Cardinal-Space-Mining/2025-Comp-Arena/Arena/AgLime.jpg

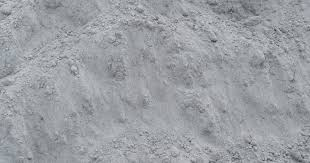
Arena/AgLime.jpg
