Cardinal-Space-Mining/2025-Comp-Arena/Arena/img/2x4s/2x4x80-HoleB.PNG

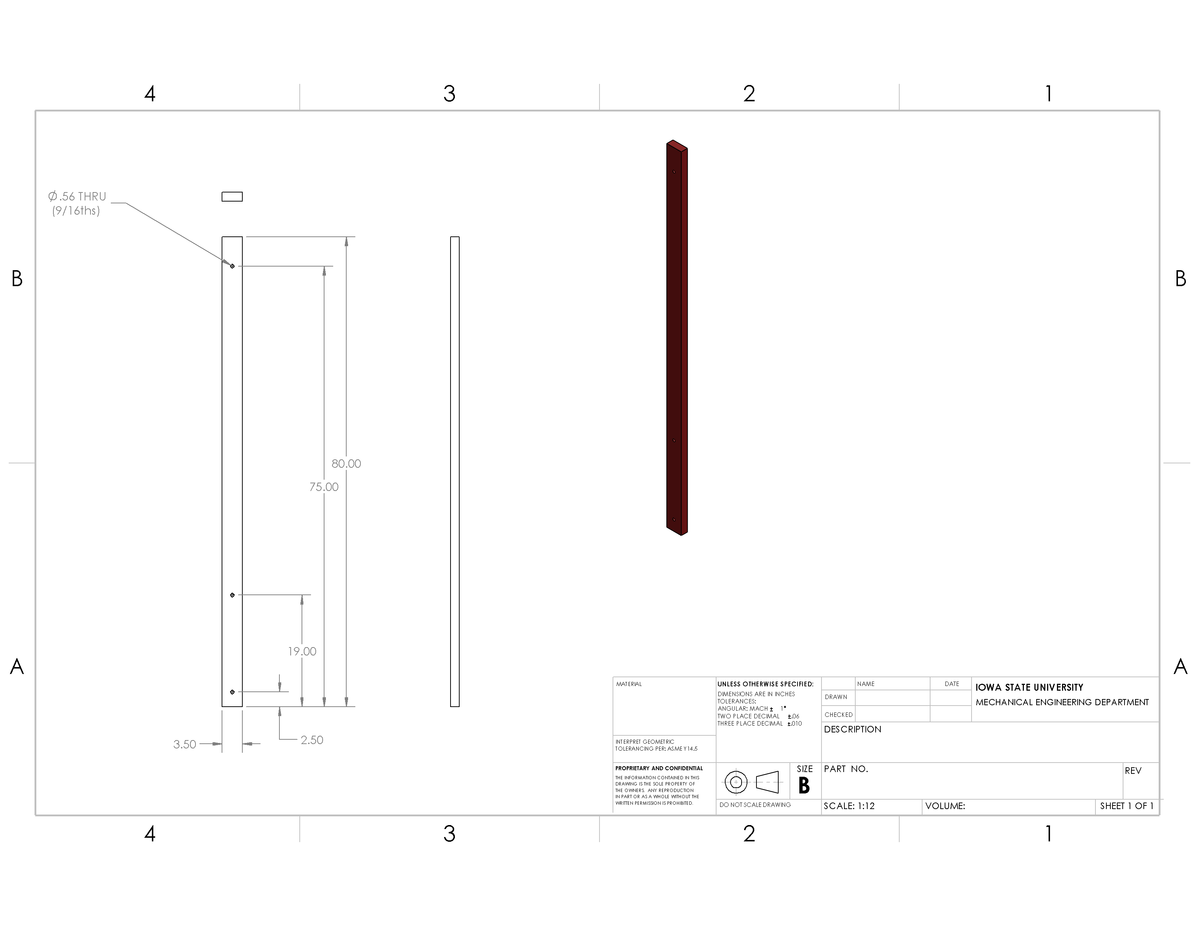
Arena/img/2x4s/2x4x80-HoleB.PNG
