Cardinal-Space-Mining/2025-Comp-Arena/HeiseSuggestions/Intake Air Filters.jpg

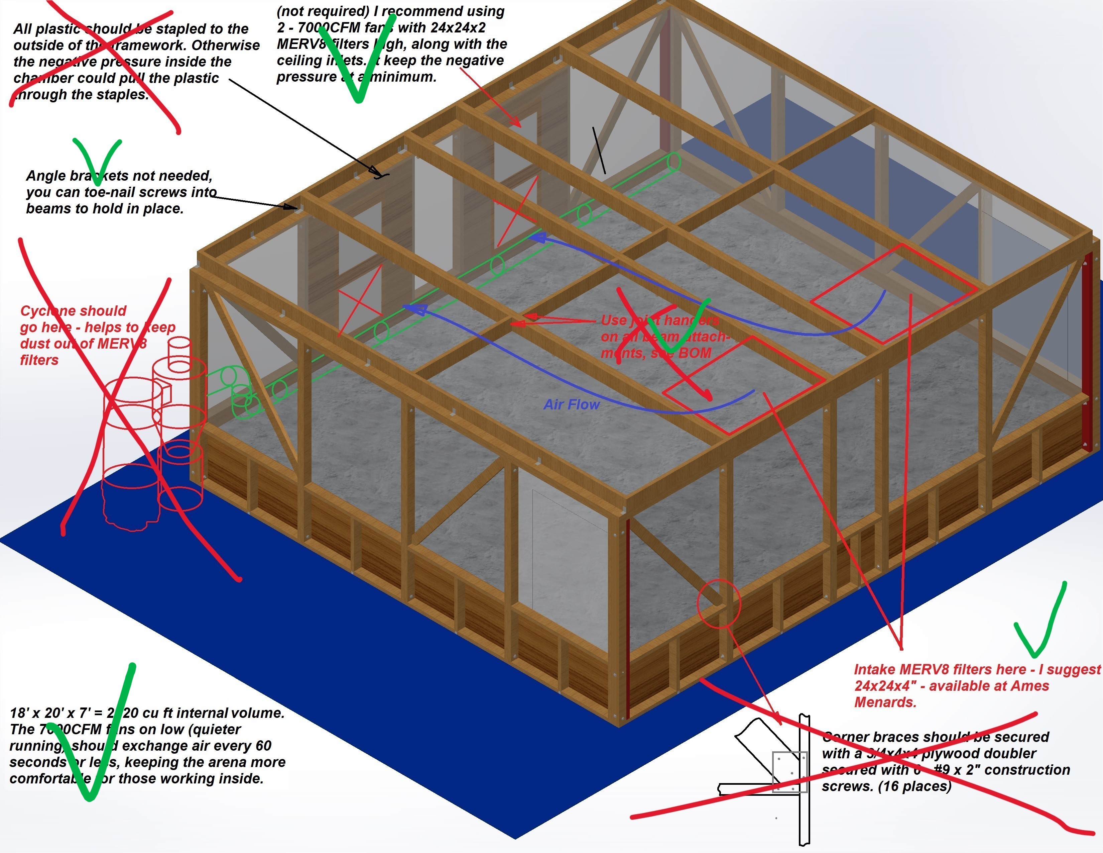
HeiseSuggestions/Intake Air Filters.jpg
