Cardinal-Space-Mining/2025-Comp-Arena/Arena/1x1s/1x1x2.SLDPRT

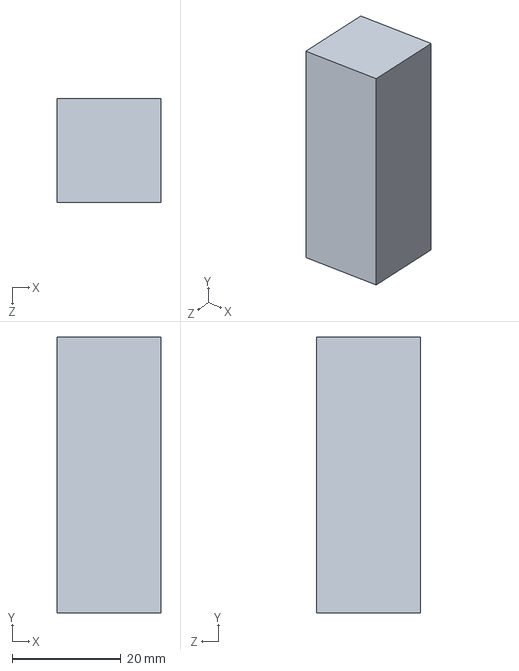
[picture p25: CAD file, 2025-01-25]
Arena/1x1s/1x1x2.SLDPRT
19.1 x 50.8 x 19.1 mm
