Cardinal-Space-Mining/2025-Comp-Arena/Arena/2x4s/2x4x80-HoleB.SLDPRT

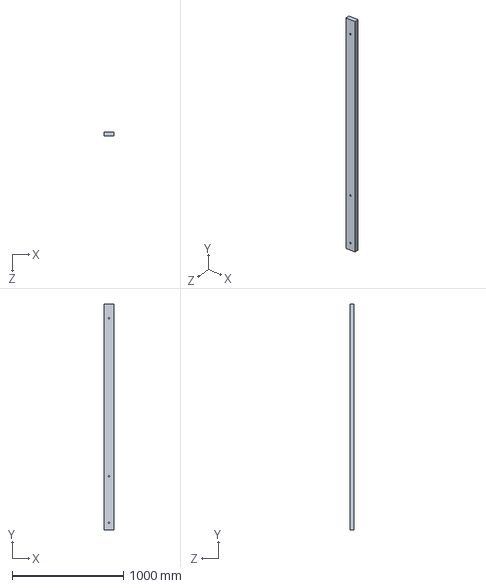
[picture p26: CAD file, 2025-03-30]
Arena/2x4s/2x4x80-HoleB.SLDPRT
88.9 x 2032.0 x 38.1 mm
