Cardinal-Space-Mining/2025-Comp-Arena/Arena/2x6s/2x6x21.SLDPRT

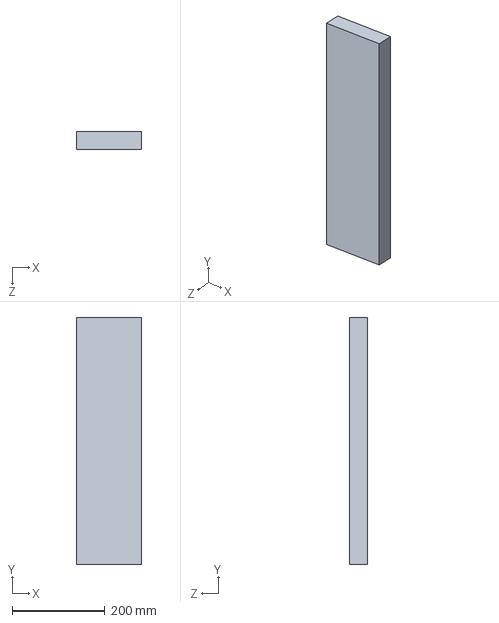
[picture p27: CAD file, 2025-03-01]
Arena/2x6s/2x6x21.SLDPRT
139.7 x 533.4 x 38.1 mm
