Cardinal-Space-Mining/2025-Comp-Arena/Arena/4x4s/4x4x83.SLDPRT

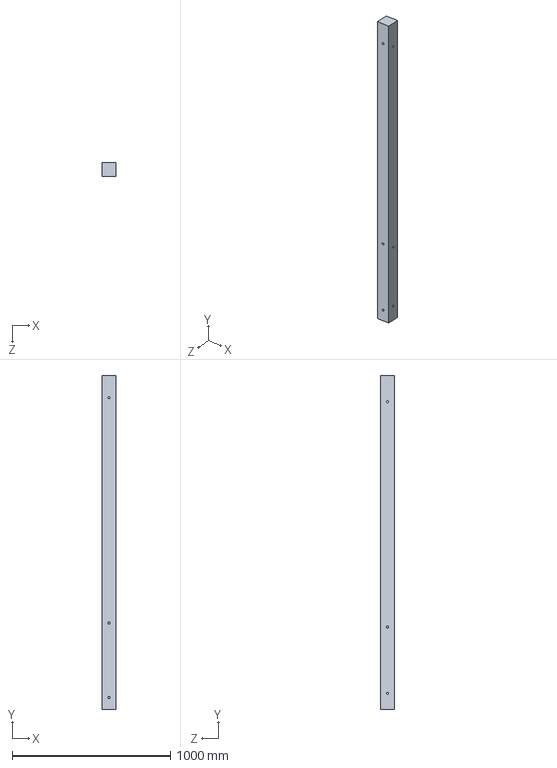
[picture p28: CAD file, 2025-03-30]
Arena/4x4s/4x4x83.SLDPRT
88.9 x 2108.2 x 88.9 mm
