Cardinal-Space-Mining/2025-Comp-Arena/Arena/filters/45x21 MERV8 Filter.SLDPRT

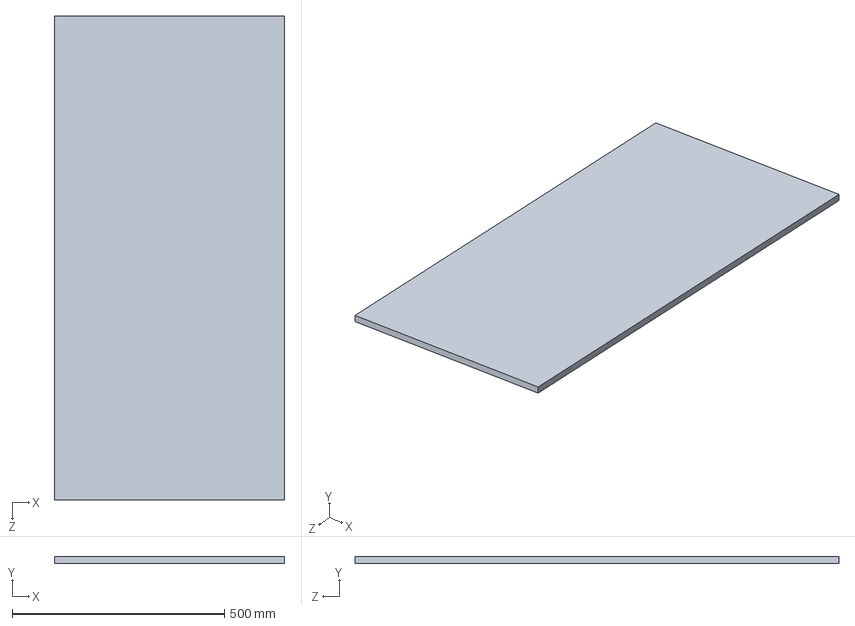
[picture p29: CAD file, 2025-05-02]
Arena/filters/45x21 MERV8 Filter.SLDPRT
541.3 x 16.5 x 1138.2 mm
