Cardinal-Space-Mining/2025-Comp-Arena/Arena/particle board/pbx24x96 particle board.SLDPRT

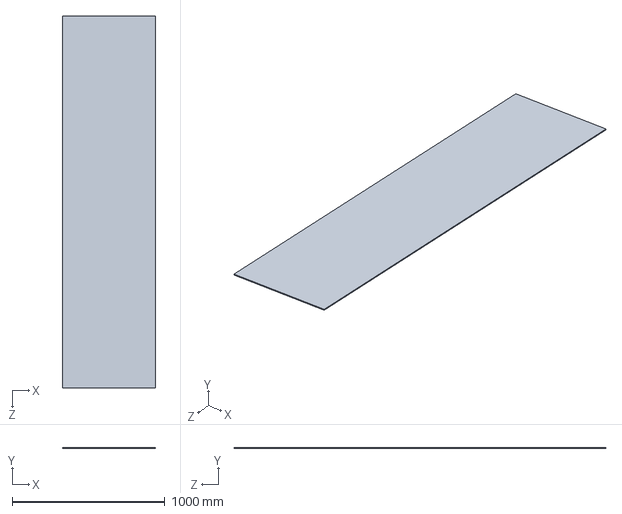
[picture p30: CAD file, 2025-03-01]
Arena/particle board/pbx24x96 particle board.SLDPRT
609.6 x 5.56 x 2438.4 mm
