Cardinal-Space-Mining/2025-Comp-Arena/Arena/plywood/plywoodx82.7x48.SLDPRT

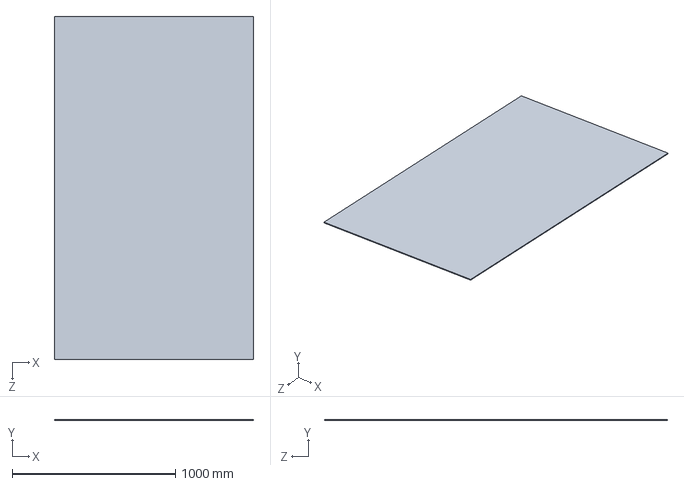
[picture p31: CAD file, 2025-05-02]
Arena/plywood/plywoodx82.7x48.SLDPRT
1219.2 x 5.56 x 2100.6 mm
