Cardinal-Space-Mining/2025-Comp-Arena/Arena/SICK/V3S##2-######A-S249638.SLDPRT

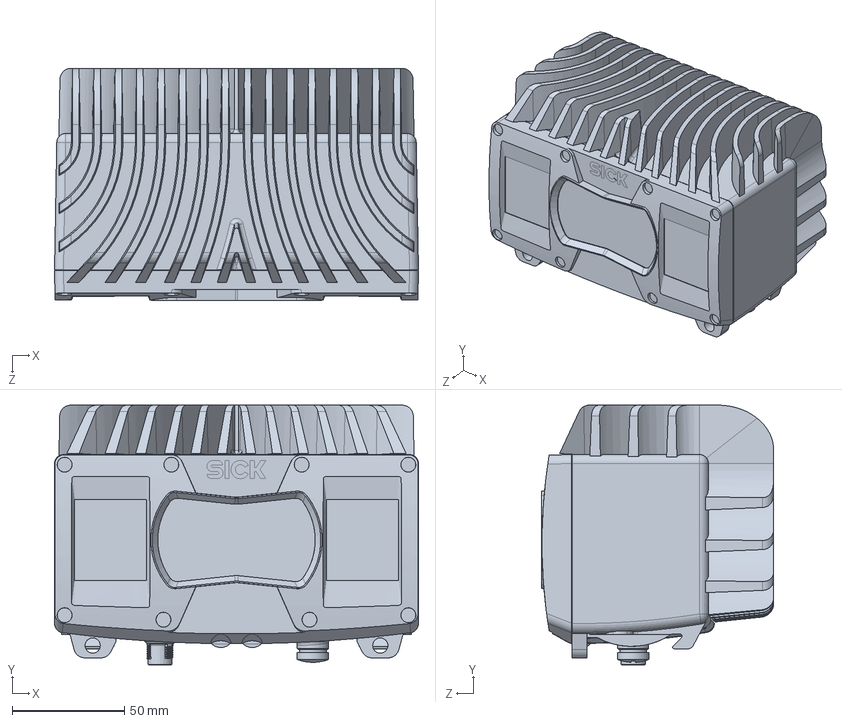
[picture p32: CAD file, 2025-03-29]
Arena/SICK/V3S##2-######A-S249638.SLDPRT
162.0 x 115.6 x 103.4 mm
