Cardinal-Space-Mining/2025-Comp-Arena/Arena/SICK_3DP_Depth_Camera_Mount.SLDPRT

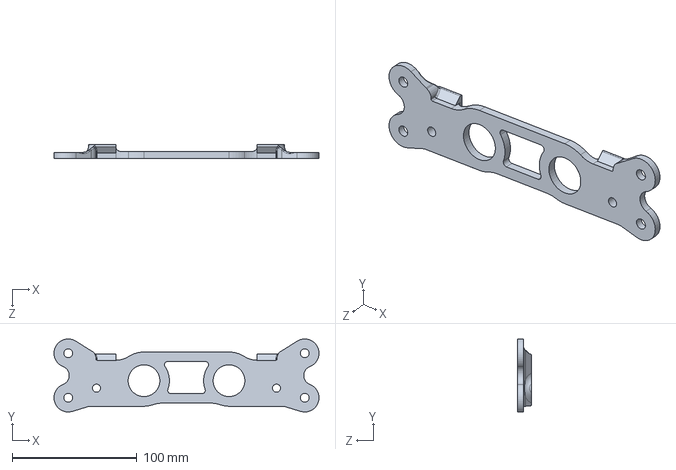
[picture p33: CAD file, 2025-05-20]
Arena/SICK_3DP_Depth_Camera_Mount.SLDPRT
212.0 x 58.4 x 11.0 mm
