Cardinal-Space-Mining/2025-Comp-Arena/Arena/strongtie/lu24.SLDPRT

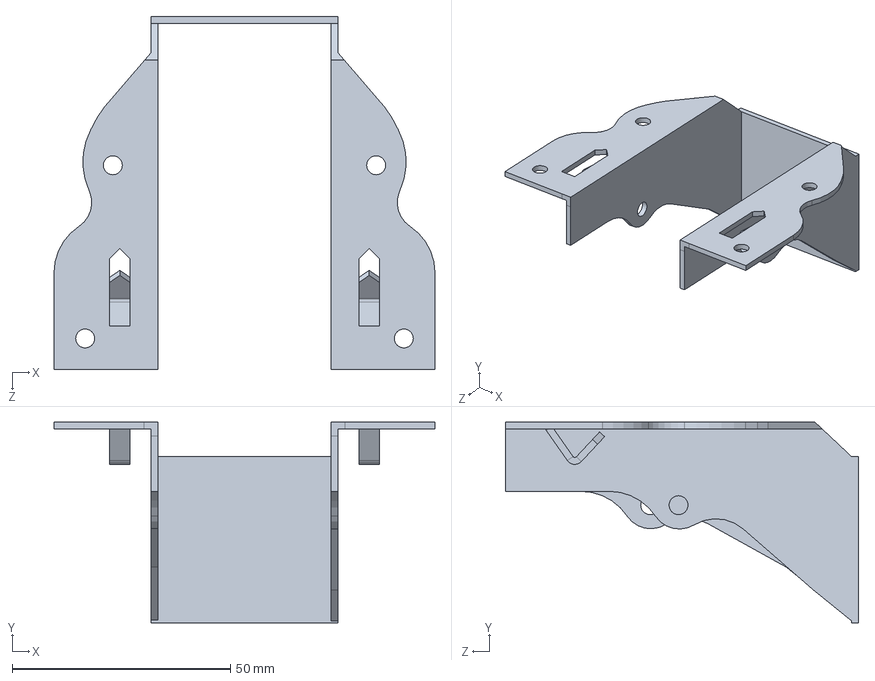
[picture p34: CAD file, 2025-05-02]
Arena/strongtie/lu24.SLDPRT
87.3 x 46.0 x 81.0 mm
