Cardinal-Space-Mining/2025-Comp-Arena/Arena/tie straps/Tie Strap 199in.SLDPRT

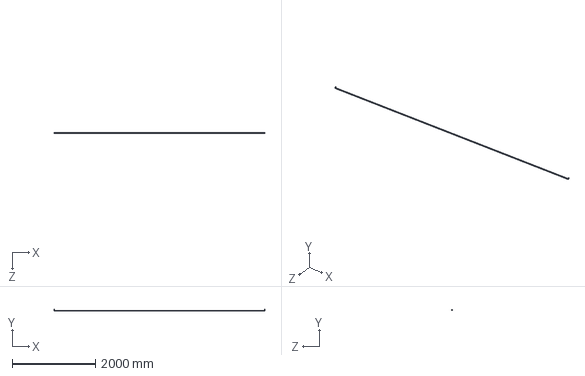
[picture p35: CAD file, 2025-03-08]
Arena/tie straps/Tie Strap 199in.SLDPRT
5055.1 x 25.7 x 25.4 mm
