Cardinal-Space-Mining/2025-Comp-Arena/Arena/vapor barriers/30x20ft Tarp.SLDPRT

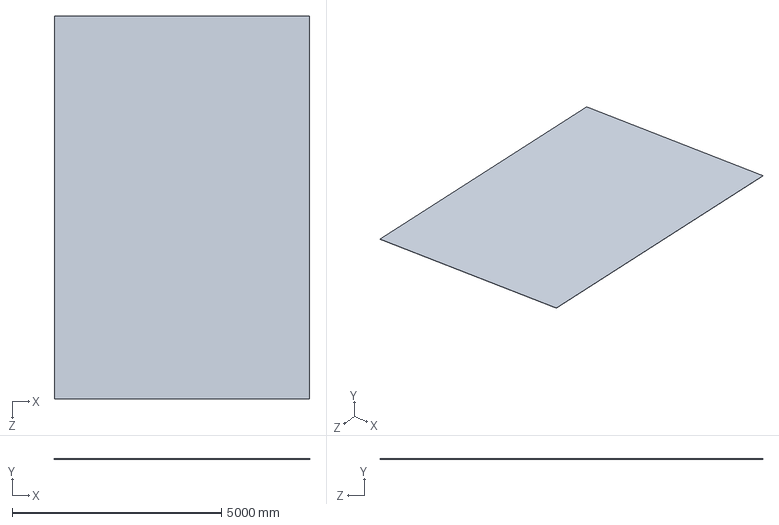
[picture p36: CAD file, 2025-03-30]
Arena/vapor barriers/30x20ft Tarp.SLDPRT
6096.0 x 6.00 x 9144.0 mm
