Cardinal-Space-Mining/2025-Comp-Arena/Arena/weatherproofing/Half Inch Weather Stripping.SLDPRT

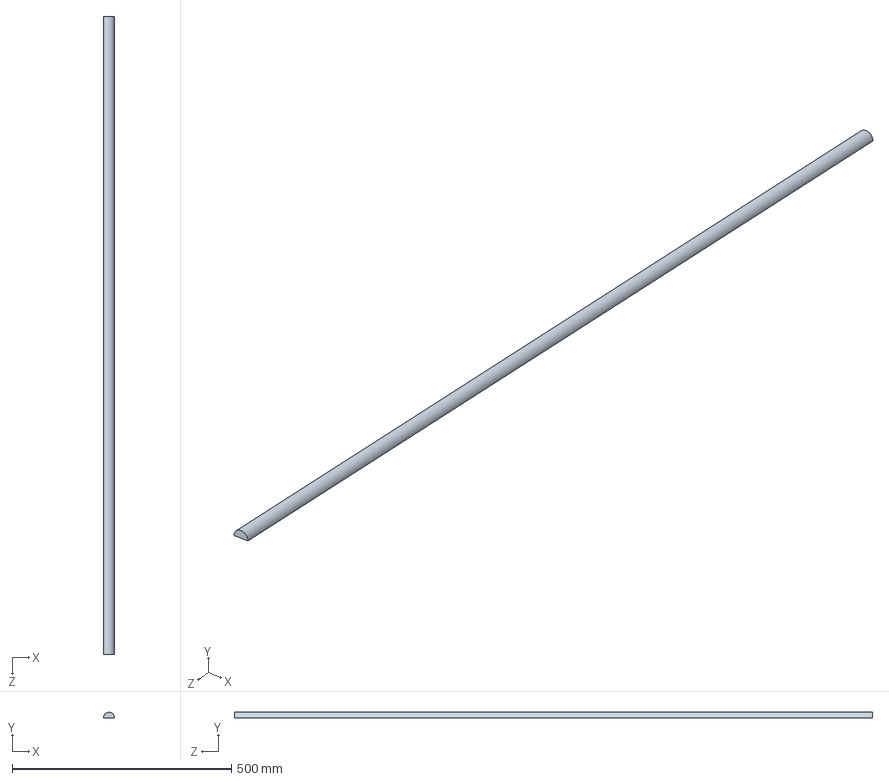
[picture p37: CAD file, 2025-01-21]
Arena/weatherproofing/Half Inch Weather Stripping.SLDPRT
25.4 x 12.7 x 1454.1 mm
