Cardinal-Space-Mining/2025-Comp-Arena/Arena/1x1s/1x1x20.11.SLDPRT

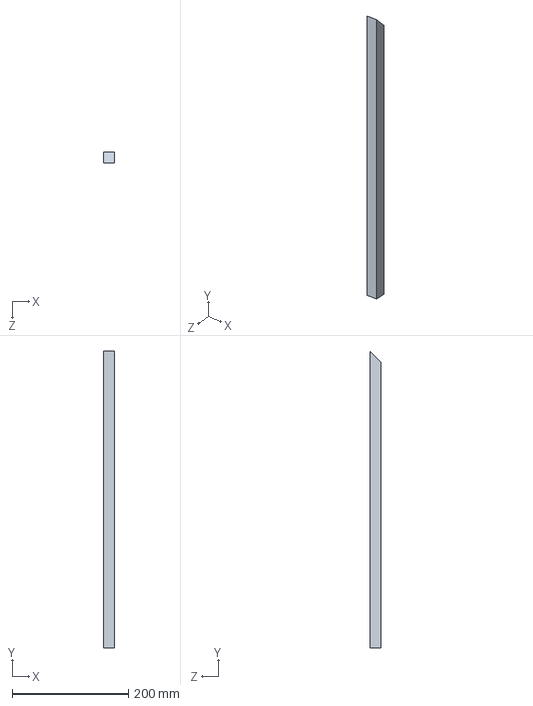
[picture p38: CAD file, 2025-01-25]
Arena/1x1s/1x1x20.11.SLDPRT
19.1 x 510.8 x 19.1 mm
