Cardinal-Space-Mining/2025-Comp-Arena/Arena/2x6s/2x6x223-Chamfered.SLDPRT

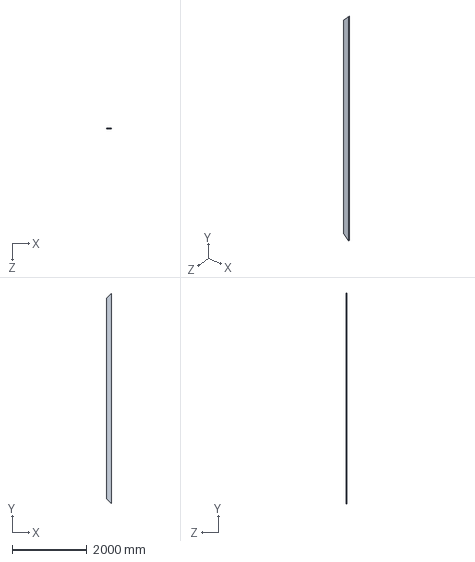
[picture p39: CAD file, 2025-03-01]
Arena/2x6s/2x6x223-Chamfered.SLDPRT
139.7 x 5664.2 x 38.1 mm
