Cardinal-Space-Mining/2025-Comp-Arena/Arena/4x4s/4x4x91.5.SLDPRT

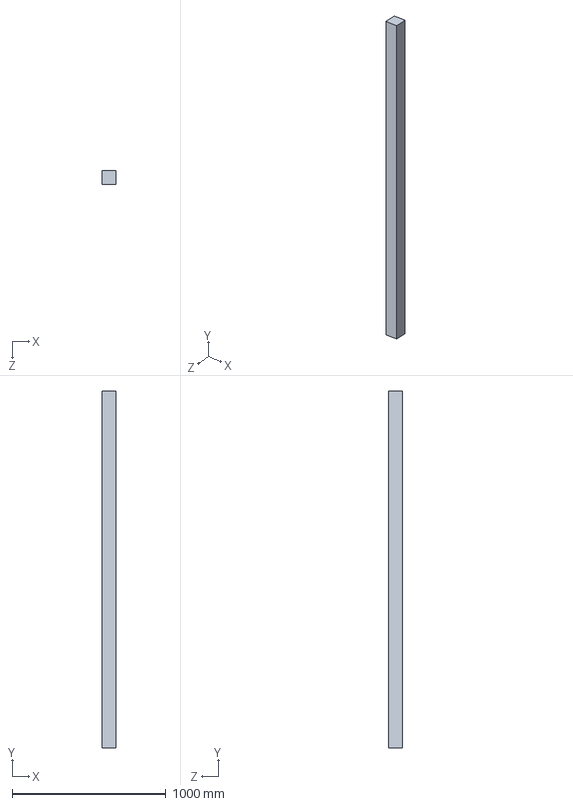
[picture p40: CAD file, 2025-01-21]
Arena/4x4s/4x4x91.5.SLDPRT
88.9 x 2324.1 x 88.9 mm
