Cardinal-Space-Mining/2025-Comp-Arena/Arena/filters/24x24 MERV8 Filter.SLDPRT

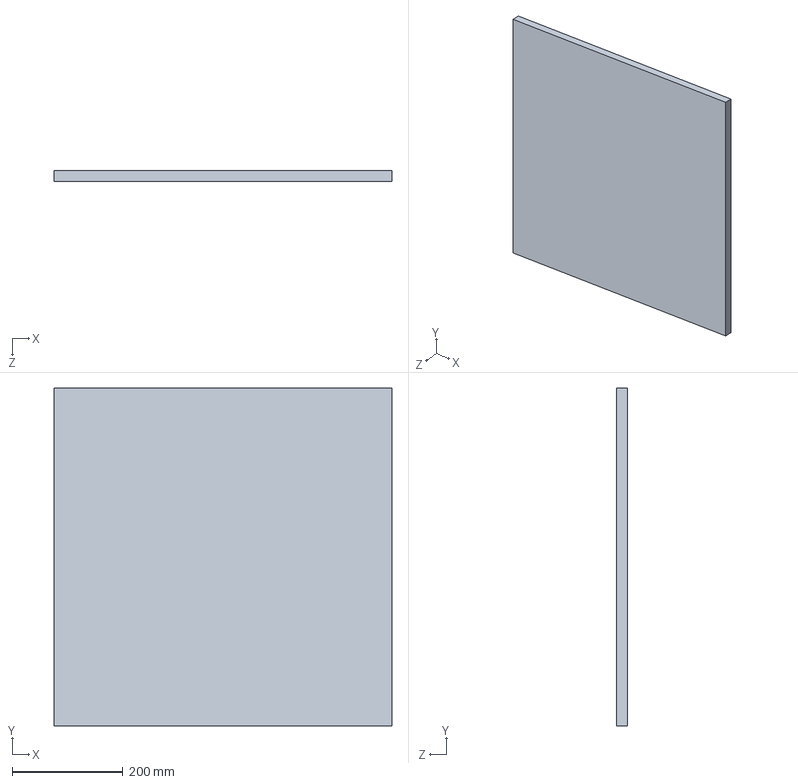
[picture p41: CAD file, 2025-01-21]
Arena/filters/24x24 MERV8 Filter.SLDPRT
609.6 x 609.6 x 19.1 mm
