Cardinal-Space-Mining/2025-Comp-Arena/Arena/plywood/plywoodx48x23.7 plywood.SLDPRT

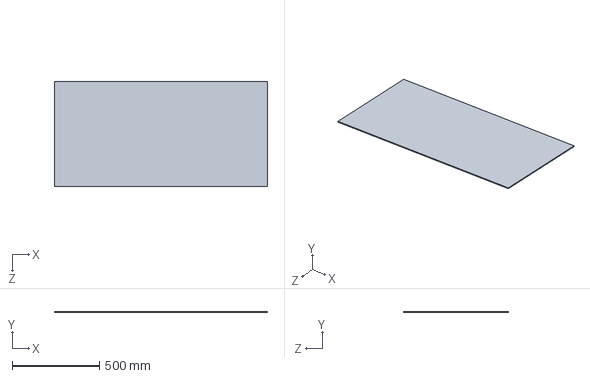
[picture p43: CAD file, 2025-03-30]
Arena/plywood/plywoodx48x23.7 plywood.SLDPRT
1219.2 x 5.56 x 602.0 mm
