Cardinal-Space-Mining/2025-Comp-Arena/Arena/strongtie/lu26.SLDPRT

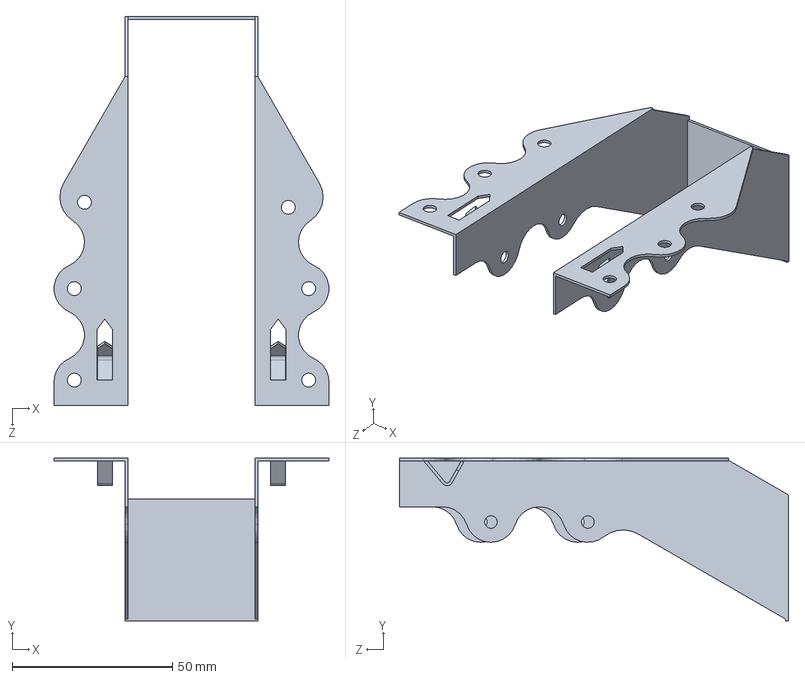
[picture p44: CAD file, 2025-05-02]
Arena/strongtie/lu26.SLDPRT
85.9 x 50.8 x 121.5 mm
