Cardinal-Space-Mining/2025-Comp-Arena/Arena/tie straps/Tie Strap 223in.SLDPRT

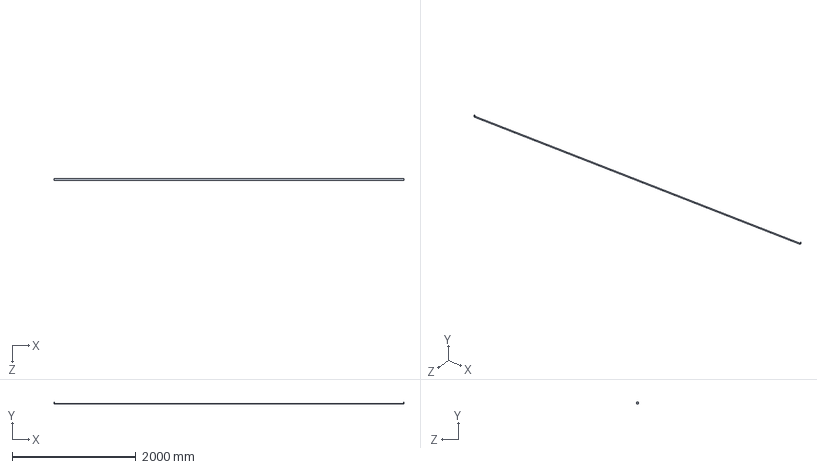
[picture p45: CAD file, 2025-03-08]
Arena/tie straps/Tie Strap 223in.SLDPRT
5664.7 x 25.7 x 25.4 mm
