Cardinal-Space-Mining/2025-Comp-Arena/Arena/vapor barriers/LZipperDoor.SLDPRT

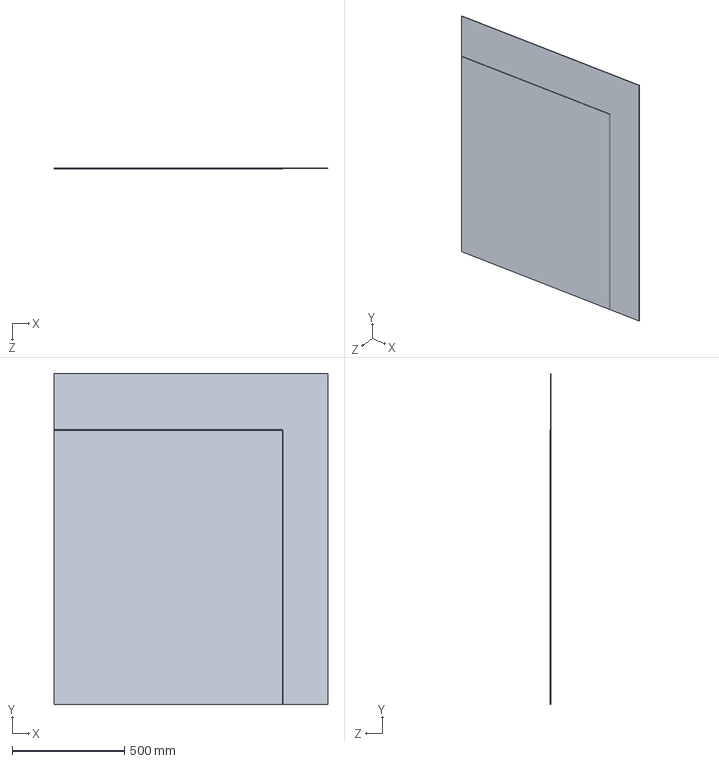
[picture p46: CAD file, 2025-03-08]
Arena/vapor barriers/LZipperDoor.SLDPRT
1219.2 x 1473.2 x 3.81 mm
