Cardinal-Space-Mining/2025-Comp-Arena/Arena/weatherproofing/Sprayfoam Seal.SLDPRT

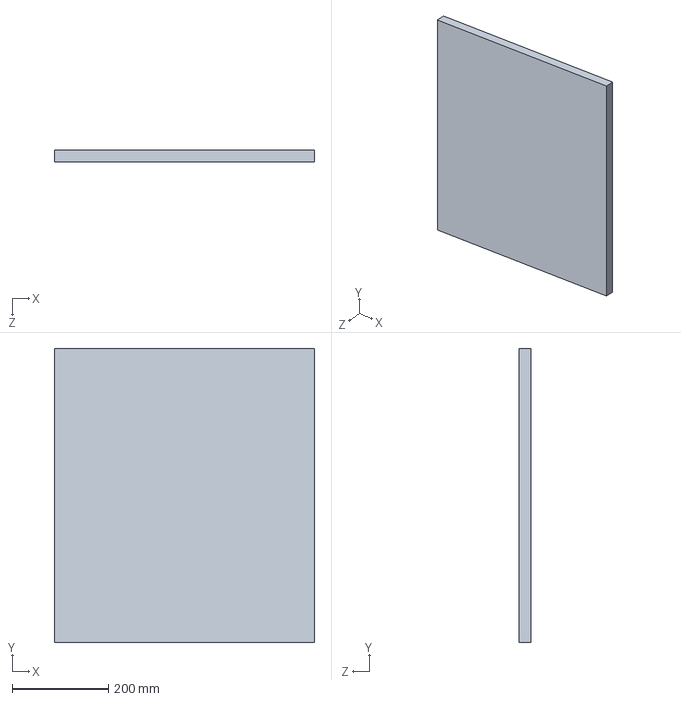
[picture p47: CAD file, 2025-01-21]
Arena/weatherproofing/Sprayfoam Seal.SLDPRT
539.8 x 609.6 x 25.4 mm
