Cardinal-Space-Mining/2025-Comp-Arena/Arena/1x1s/1x1x31.SLDPRT

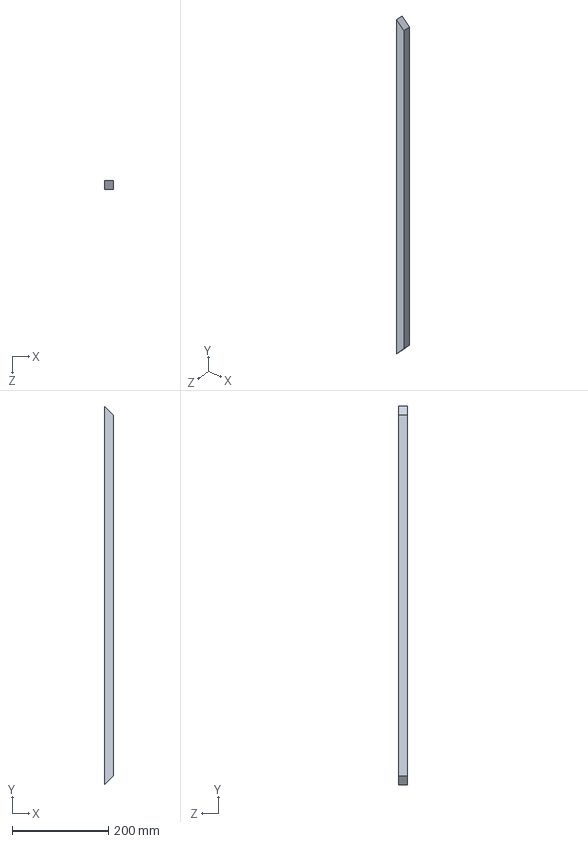
[picture p48: CAD file, 2025-01-25]
Arena/1x1s/1x1x31.SLDPRT
19.1 x 787.4 x 19.1 mm
