Cardinal-Space-Mining/2025-Comp-Arena/Arena/2x4s/2x4x73.02.SLDPRT

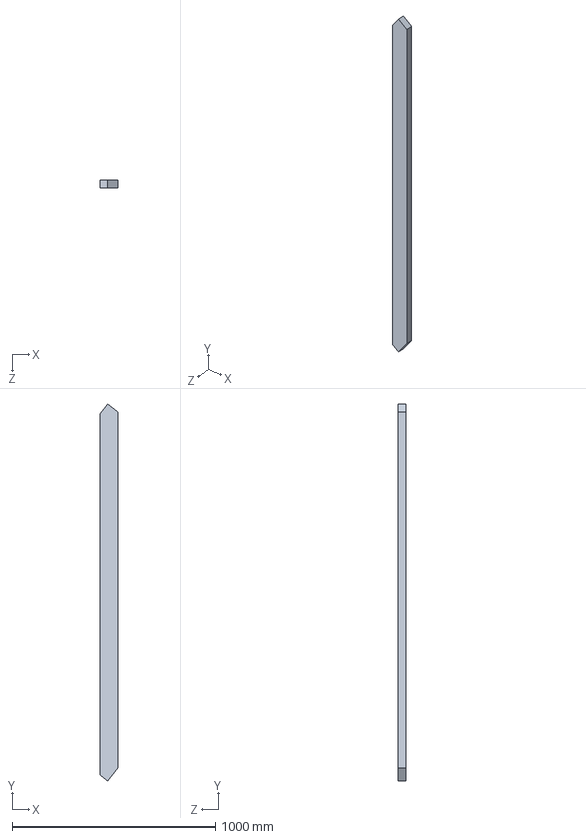
[picture p49: CAD file, 2025-01-25]
Arena/2x4s/2x4x73.02.SLDPRT
88.9 x 1854.6 x 38.1 mm
