Cardinal-Space-Mining/2025-Comp-Arena/Arena/2x6s/2x6x24.SLDPRT

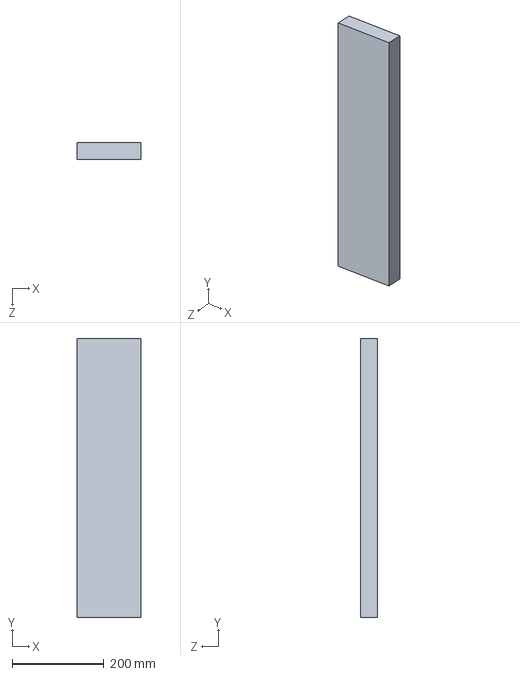
[picture p50: CAD file, 2025-03-01]
Arena/2x6s/2x6x24.SLDPRT
139.7 x 609.6 x 38.1 mm
