Cardinal-Space-Mining/2025-Comp-Arena/Arena/particle board/pbx48x48 particle board.SLDPRT

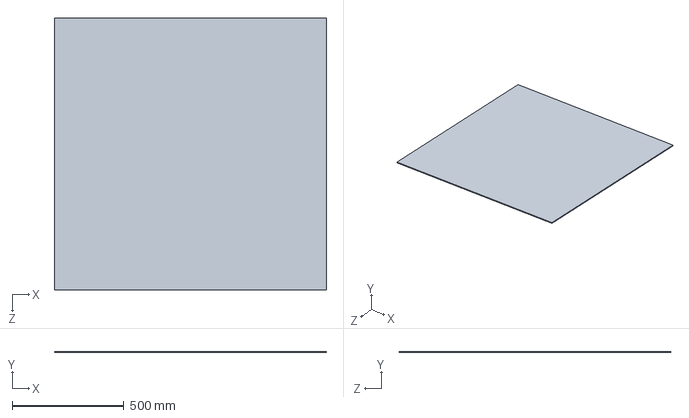
[picture p51: CAD file, 2025-01-21]
Arena/particle board/pbx48x48 particle board.SLDPRT
1219.2 x 5.56 x 1219.2 mm
