Cardinal-Space-Mining/2025-Comp-Arena/Arena/plywood/plywoodxshelf plywood.SLDPRT

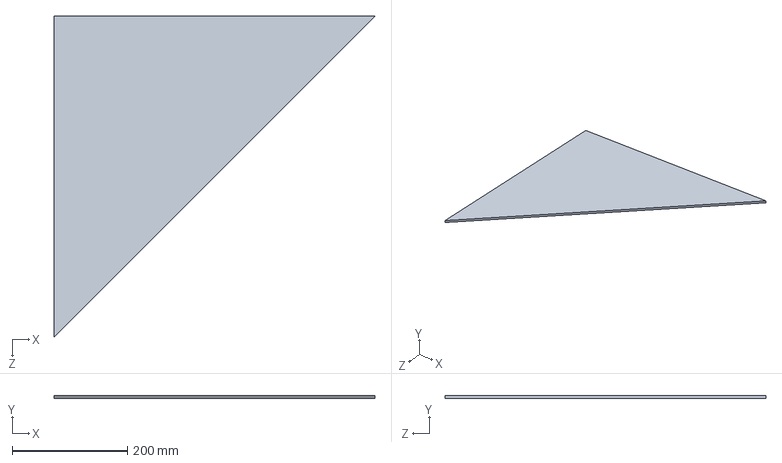
[picture p52: CAD file, 2025-03-30]
Arena/plywood/plywoodxshelf plywood.SLDPRT
556.8 x 5.56 x 556.8 mm
