Cardinal-Space-Mining/2025-Comp-Arena/Arena/strongtie/TP35.SLDPRT

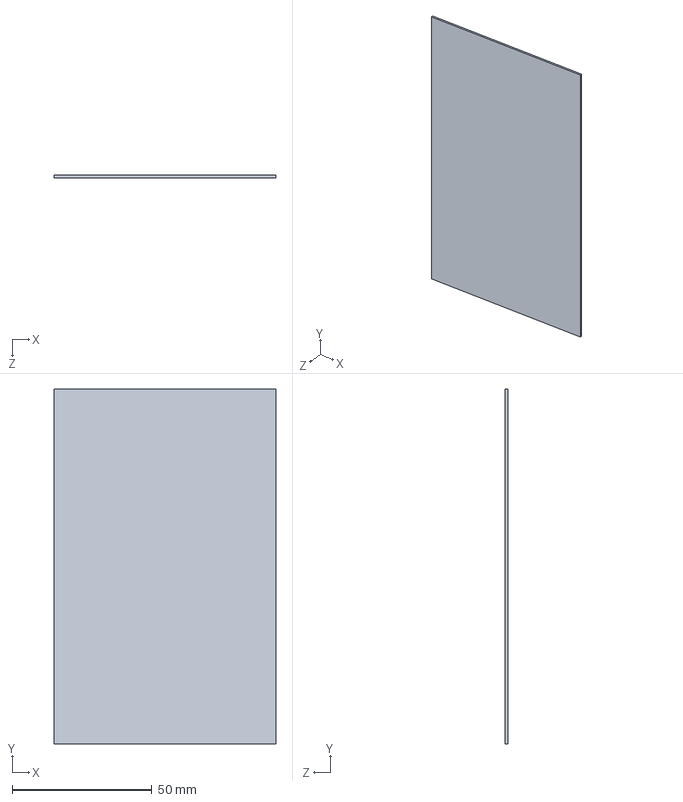
[picture p53: CAD file, 2025-03-01]
Arena/strongtie/TP35.SLDPRT
79.4 x 127.0 x 0.912 mm
