Cardinal-Space-Mining/2025-Comp-Arena/Arena/vapor barriers/plastic sheeting 216x192.SLDPRT

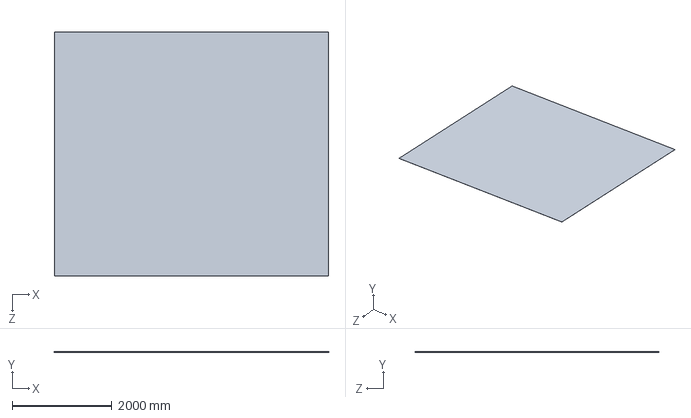
[picture p54: CAD file, 2025-03-01]
Arena/vapor barriers/plastic sheeting 216x192.SLDPRT
5486.4 x 1.59 x 4876.8 mm
