Cardinal-Space-Mining/2025-Comp-Arena/Arena/1x1s/1x1x3.SLDPRT

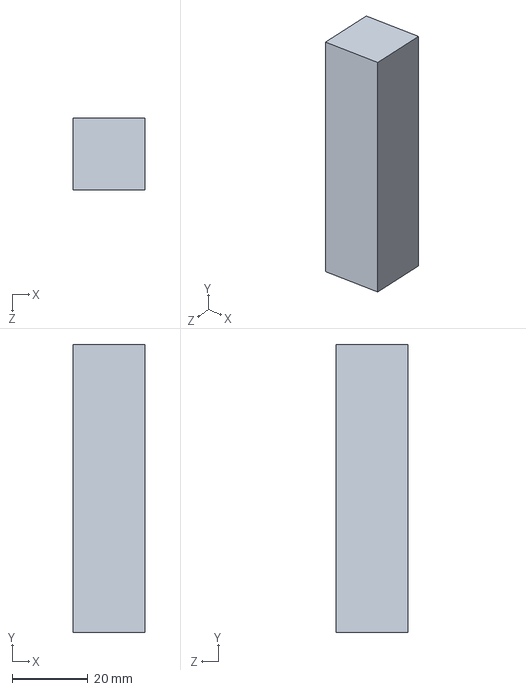
[picture p55: CAD file, 2025-01-21]
Arena/1x1s/1x1x3.SLDPRT
19.1 x 76.2 x 19.1 mm
