Cardinal-Space-Mining/2025-Comp-Arena/Arena/2x4s/2x4x88.5.SLDPRT

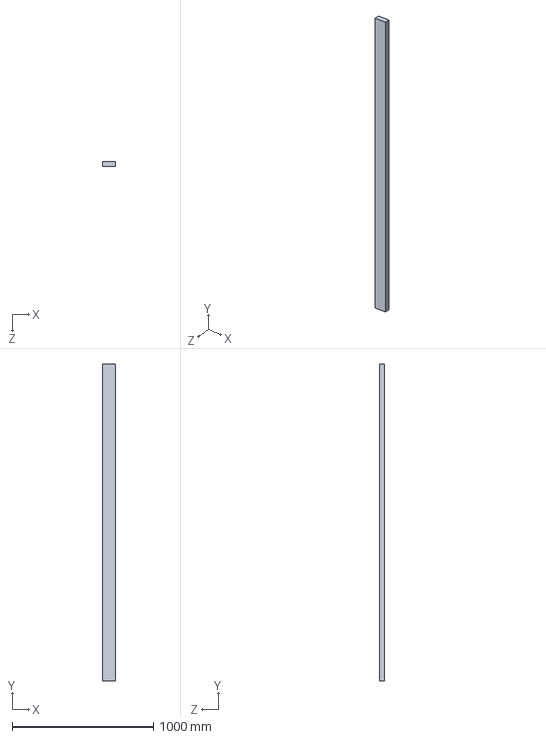
[picture p56: CAD file, 2025-01-21]
Arena/2x4s/2x4x88.5.SLDPRT
88.9 x 2247.9 x 38.1 mm
