Cardinal-Space-Mining/2025-Comp-Arena/Arena/2x6s/2x6x96.SLDPRT

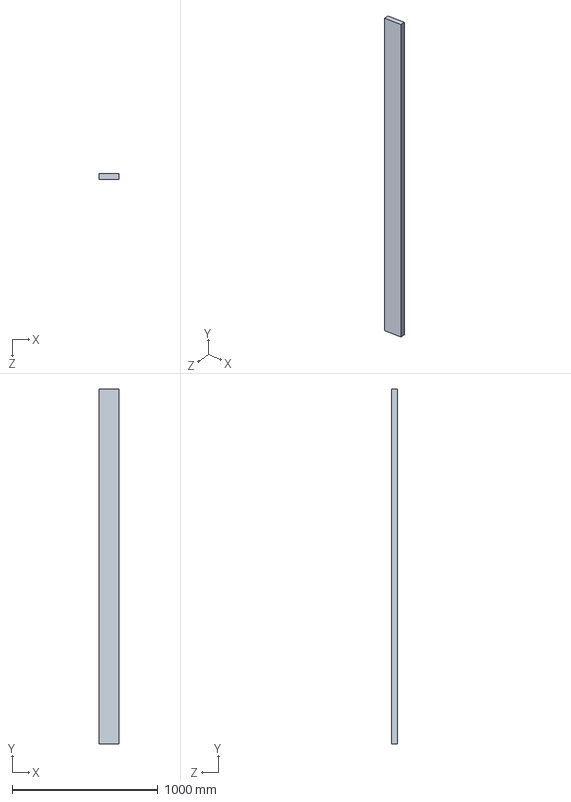
[picture p57: CAD file, 2025-01-21]
Arena/2x6s/2x6x96.SLDPRT
139.7 x 2438.4 x 38.1 mm
