Cardinal-Space-Mining/2025-Comp-Arena/Arena/Comp. Room.SLDPRT

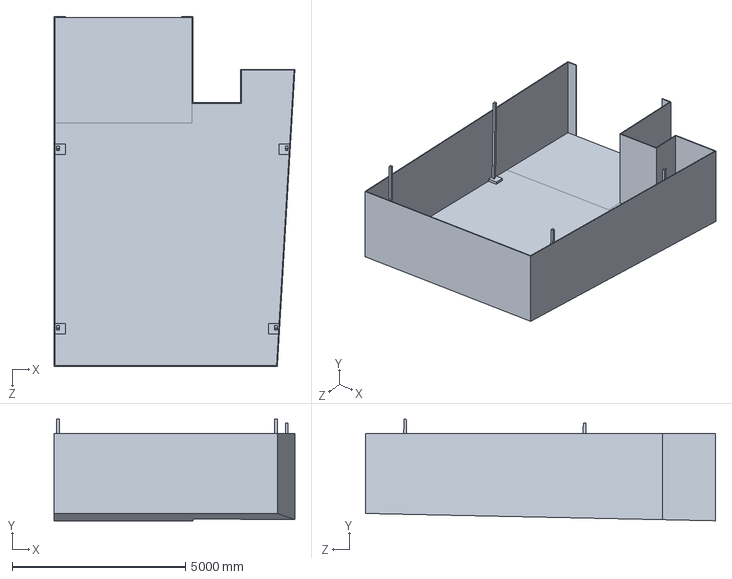
[picture p58: CAD file, 2025-05-02]
Arena/Comp. Room.SLDPRT
6959.6 x 2934.1 x 10109.2 mm
