Cardinal-Space-Mining/2025-Comp-Arena/Arena/plywood/plywoodx24x23.7 plywood.SLDPRT

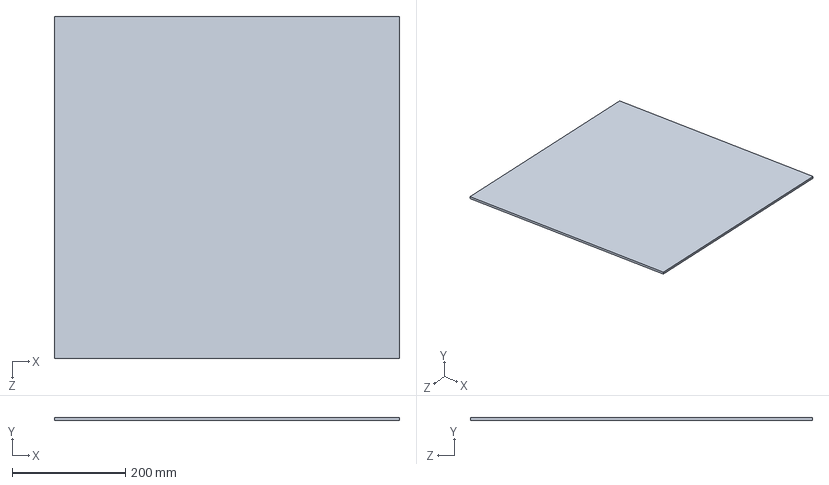
[picture p59: CAD file, 2025-03-30]
Arena/plywood/plywoodx24x23.7 plywood.SLDPRT
609.6 x 5.56 x 603.9 mm
