Cardinal-Space-Mining/2025-Comp-Arena/Arena/strongtie/A21Z.SLDPRT

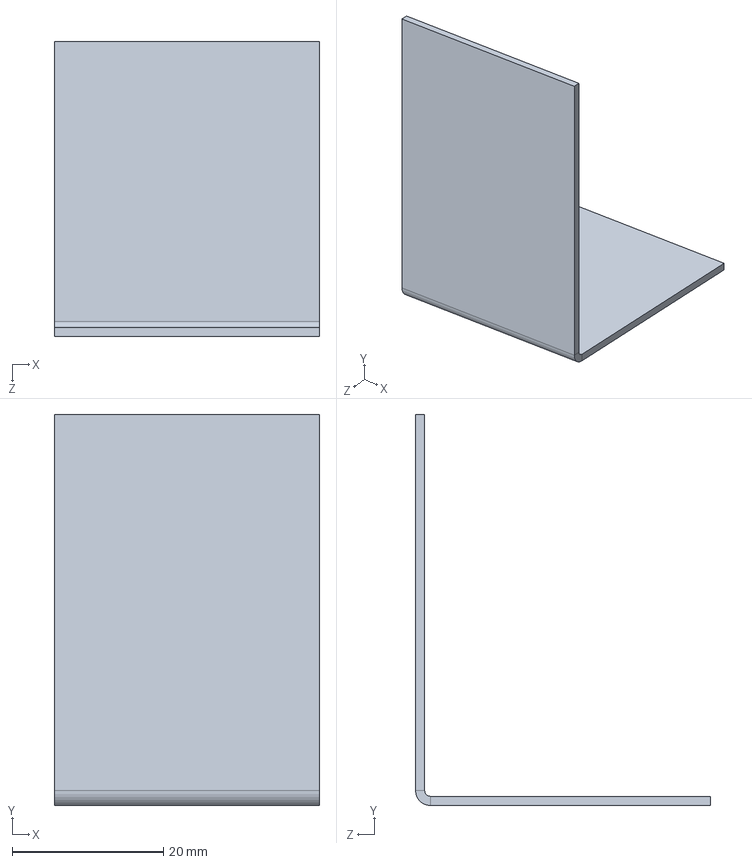
[picture p60: CAD file, 2025-01-21]
Arena/strongtie/A21Z.SLDPRT
35.1 x 51.7 x 39.0 mm
