Cardinal-Space-Mining/2025-Comp-Arena/Arena/2x4s/2x4x24.SLDPRT

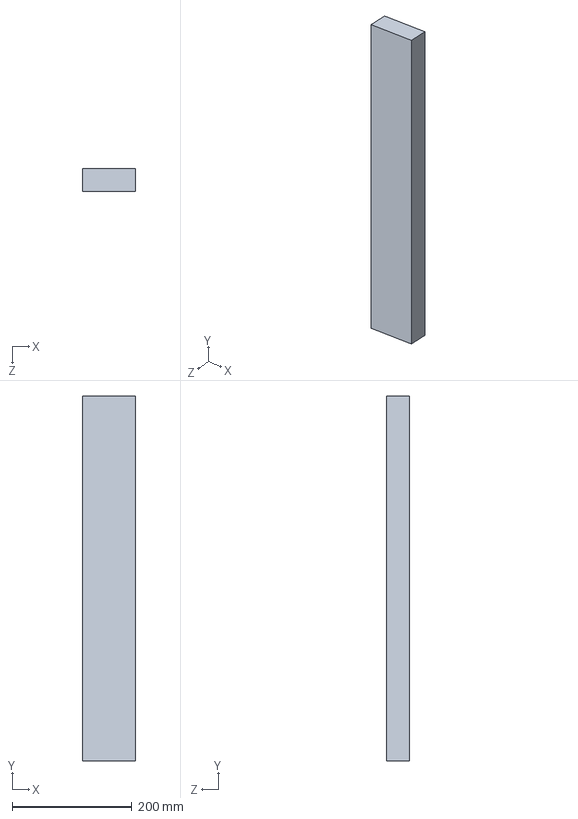
[picture p62: CAD file, 2025-01-21]
Arena/2x4s/2x4x24.SLDPRT
88.9 x 609.6 x 38.1 mm
