Cardinal-Space-Mining/2025-Comp-Arena/Arena/plywood/plywoodx48x24 plywood.SLDPRT

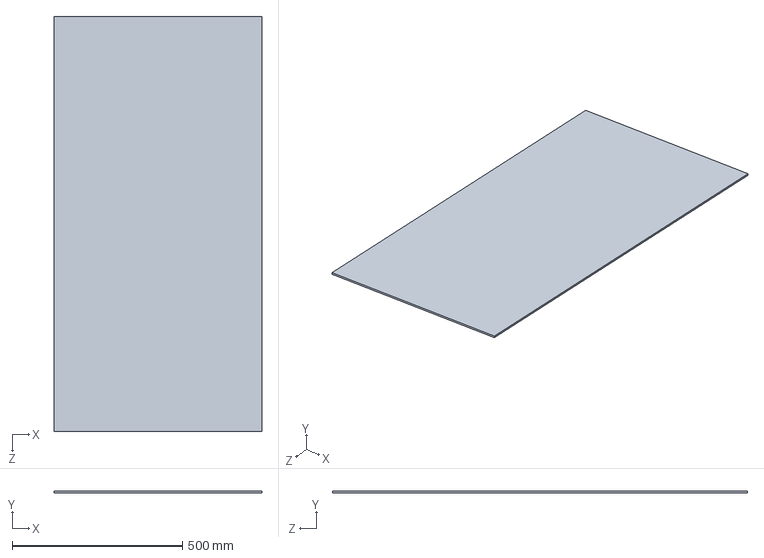
[picture p63: CAD file, 2025-03-01]
Arena/plywood/plywoodx48x24 plywood.SLDPRT
609.6 x 5.56 x 1219.2 mm
