Cardinal-Space-Mining/2025-Comp-Arena/Arena/vapor barriers/plastic sheeting 216x82.78-fan.SLDPRT

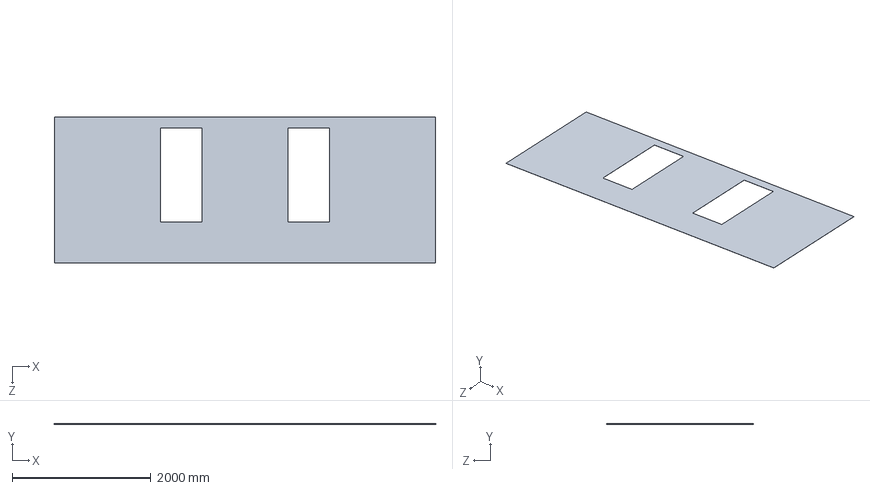
[picture p64: CAD file, 2025-03-01]
Arena/vapor barriers/plastic sheeting 216x82.78-fan.SLDPRT
5486.4 x 1.59 x 2102.6 mm
