Cardinal-Space-Mining/2025-Comp-Arena/Arena/2x4s/2x4x45.SLDPRT

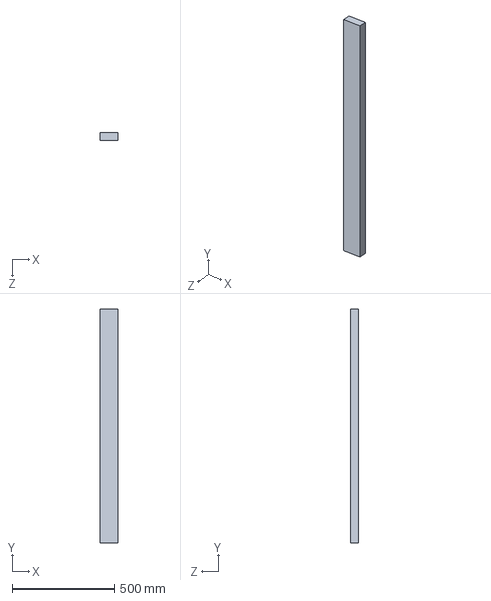
[picture p65: CAD file, 2025-01-21]
Arena/2x4s/2x4x45.SLDPRT
88.9 x 1143.0 x 38.1 mm
