Cardinal-Space-Mining/2025-Comp-Arena/Arena/2x6s/2x6x196.SLDPRT

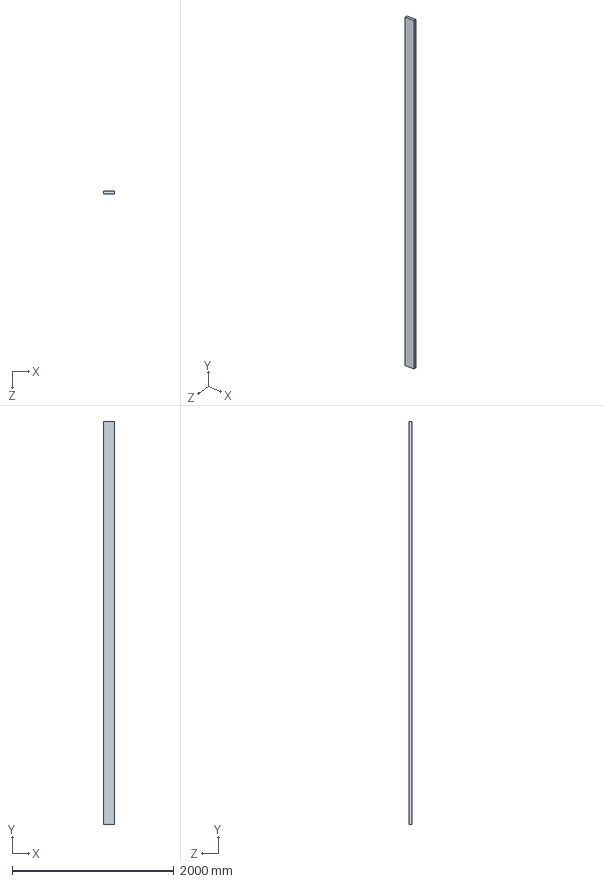
[picture p66: CAD file, 2025-01-21]
Arena/2x6s/2x6x196.SLDPRT
139.7 x 4978.4 x 38.1 mm
