Cardinal-Space-Mining/2025-Comp-Arena/Arena/plywood/plywoodx44.375x57.25.SLDPRT

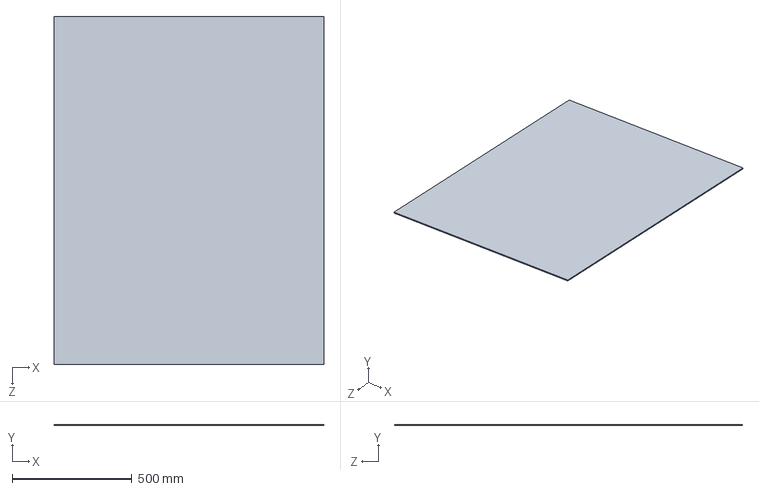
[picture p67: CAD file, 2025-01-21]
Arena/plywood/plywoodx44.375x57.25.SLDPRT
1127.1 x 5.56 x 1454.1 mm
