Cardinal-Space-Mining/2025-Comp-Arena/Arena/Regolith.SLDPRT

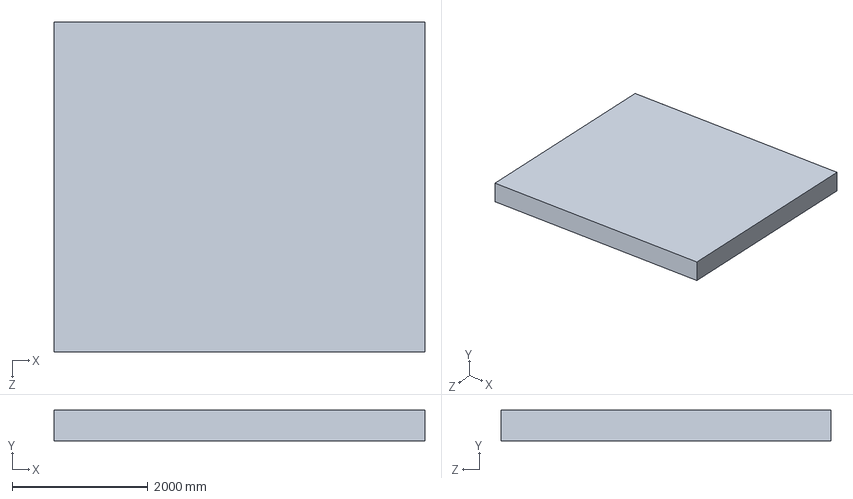
[picture p68: CAD file, 2025-01-26]
Arena/Regolith.SLDPRT
5475.2 x 457.2 x 4865.6 mm
