Cardinal-Space-Mining/2025-Comp-Arena/Arena/vapor barriers/plastic sheeting door.SLDPRT

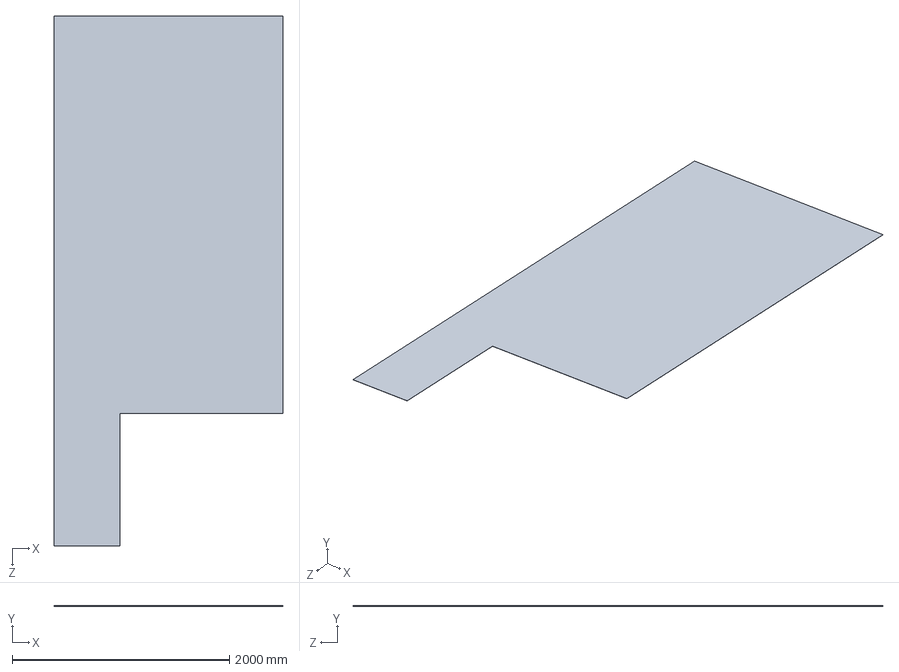
[picture p69: CAD file, 2025-01-21]
Arena/vapor barriers/plastic sheeting door.SLDPRT
2102.6 x 1.59 x 4876.8 mm
