Cardinal-Space-Mining/2025-Comp-Arena/Arena/2x4s/2x4x65.75.SLDPRT

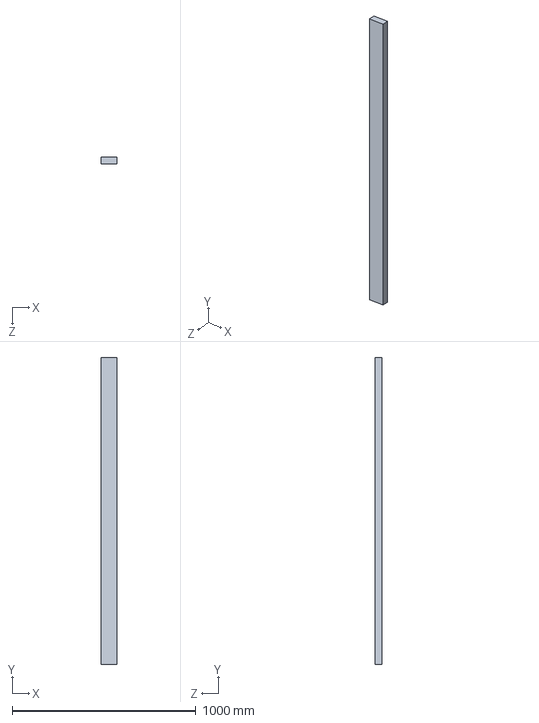
[picture p70: CAD file, 2025-01-21]
Arena/2x4s/2x4x65.75.SLDPRT
88.9 x 1670.1 x 38.1 mm
