Cardinal-Space-Mining/2025-Comp-Arena/Arena/2x6s/2x6x199-Chamfered.SLDPRT

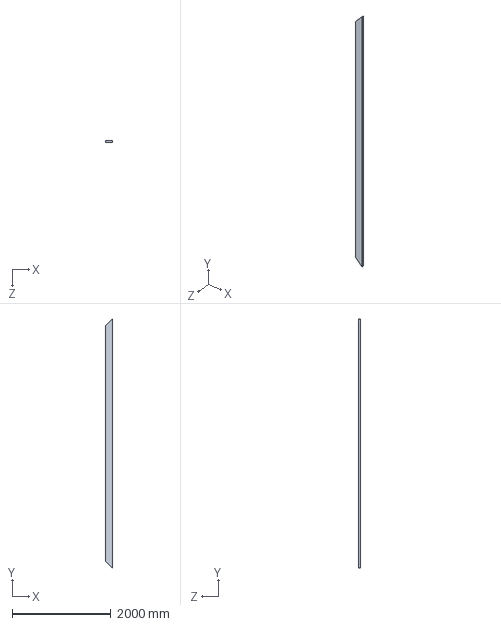
[picture p71: CAD file, 2025-01-21]
Arena/2x6s/2x6x199-Chamfered.SLDPRT
139.7 x 5054.6 x 38.1 mm
