Cardinal-Space-Mining/2025-Comp-Arena/Arena/RegolithLayout.SLDPRT

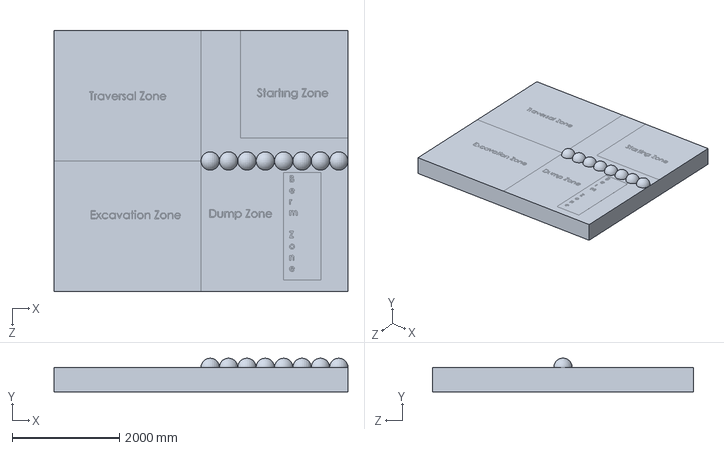
[picture p72: CAD file, 2025-01-26]
Arena/RegolithLayout.SLDPRT
5475.2 x 627.5 x 4865.6 mm
