Cardinal-Space-Mining/2025-Comp-Arena/Arena/2x4s/2x4x48.SLDPRT

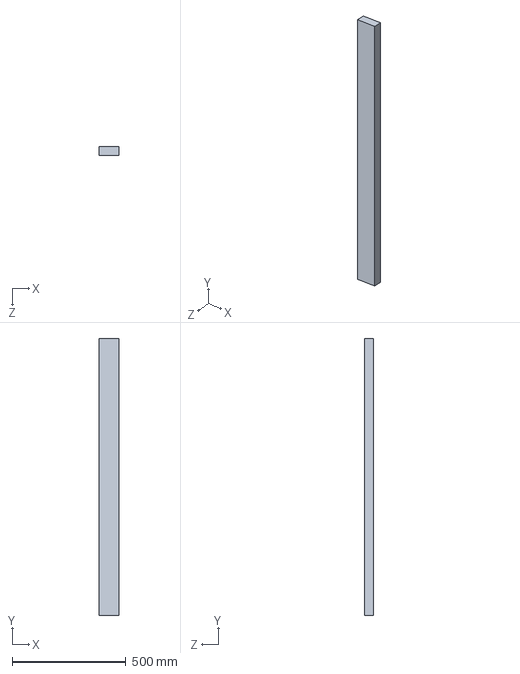
[picture p74: CAD file, 2025-01-21]
Arena/2x4s/2x4x48.SLDPRT
88.9 x 1219.2 x 38.1 mm
