Cardinal-Space-Mining/2025-Comp-Arena/Arena/2x6s/2x6x48.SLDPRT

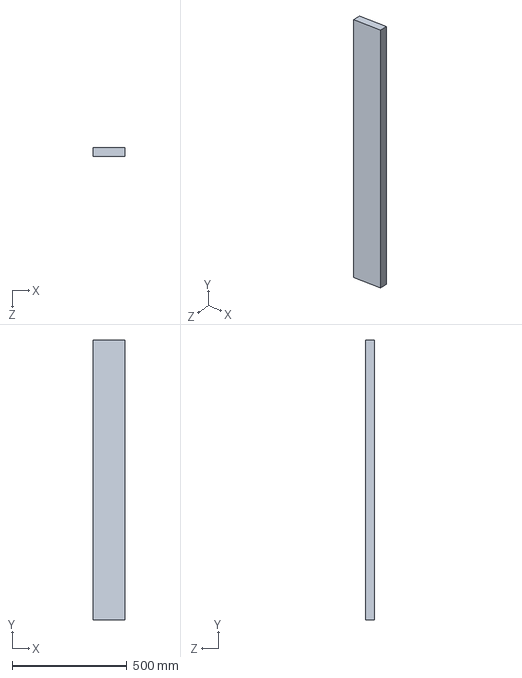
[picture p75: CAD file, 2025-01-21]
Arena/2x6s/2x6x48.SLDPRT
139.7 x 1219.2 x 38.1 mm
