Cardinal-Space-Mining/2025-Comp-Arena/Arena/2x6s/2x6x45.SLDPRT

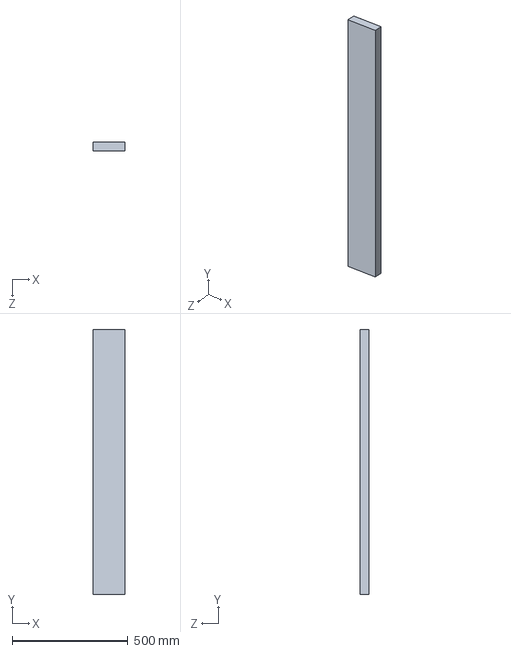
[picture p77: CAD file, 2025-01-21]
Arena/2x6s/2x6x45.SLDPRT
139.7 x 1143.0 x 38.1 mm
