Cardinal-Space-Mining/2025-Comp-Arena/Arena/2x4s/2x4x41.375.SLDPRT

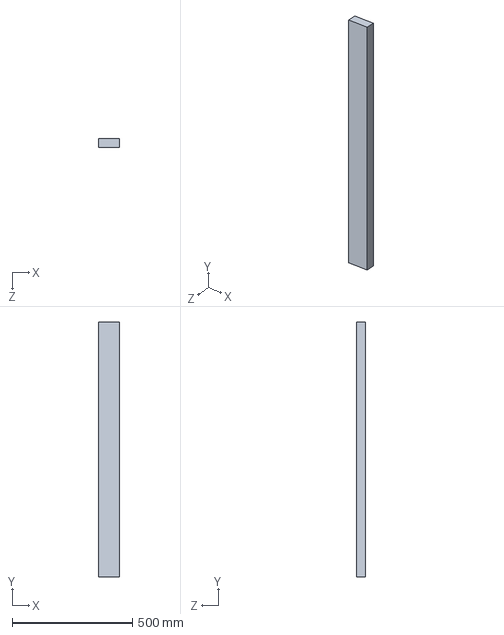
[picture p78: CAD file, 2025-01-21]
Arena/2x4s/2x4x41.375.SLDPRT
88.9 x 1060.4 x 38.1 mm
