Cardinal-Space-Mining/2025-Comp-Arena/Arena/ArenaPannelForm.SLDASM

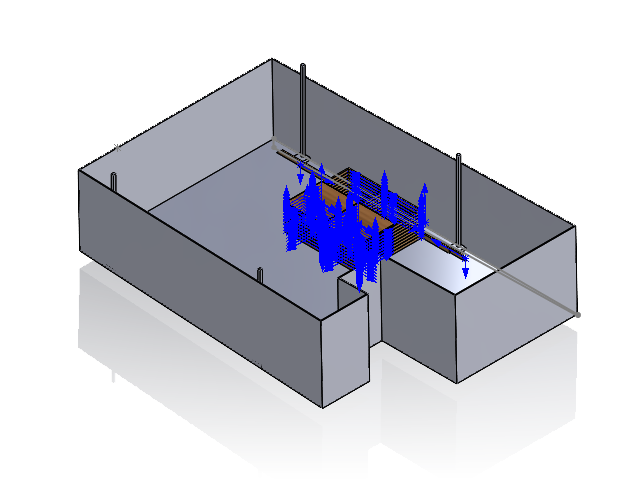
[picture p90: CAD file, 2025-01-25]
Arena/ArenaPannelForm.SLDASM
2x4x48 x 36
2x4x21 x 18
2x4x45 x 18
plywoodx48x23.775 plywood x 18
2x4x80-Hole x 36
plywoodx48x48 plywood x 18
2x6x196
2x6x247-Chamfered
Comp. Room
