Cardinal-Space-Mining/2025-Comp-Arena/Arena/walls/crown.SLDASM

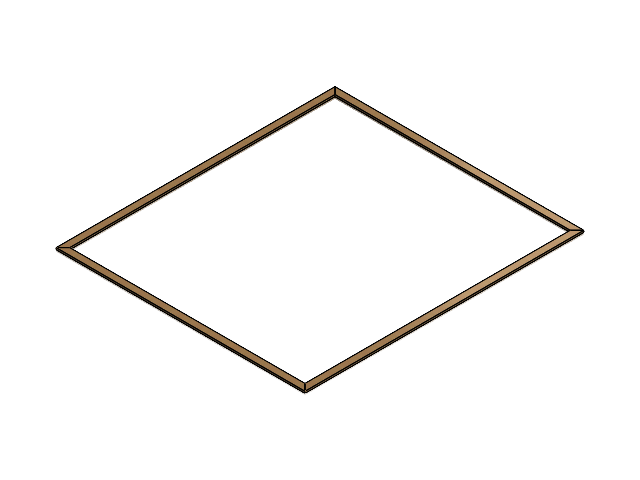
[picture p91: CAD file, 2025-03-30]
Arena/walls/crown.SLDASM
2x6x199-Chamfered x 2
2x6x223-Chamfered x 2
